pbozeman/vanilla-ice40/examples/gfx/gfx_top.v

`ifndef GFX_TOP_V
`define GFX_TOP_V

// Super basic hello world of a line.
// Output coordinates to io pins, no display, for now.

`include "directives.v"

`include "initial_reset.v"
`include "gfx_line.v"

module gfx_top #(
    parameter VGA_WIDTH  = 640,
    parameter VGA_HEIGHT = 480
) (
    // board signals
    input  wire CLK,
    output wire LED1,
    output wire LED2,

    output wire [7:0] R_E,
    output wire [7:0] R_F,

    output wire [7:0] R_H,
    output wire [7:0] R_I
);
  localparam FB_X_BITS = $clog2(VGA_WIDTH);
  localparam FB_Y_BITS = $clog2(VGA_HEIGHT);

  reg                 reset;

  reg                 enable;
  reg                 start;
  reg [FB_X_BITS-1:0] x0;
  reg [FB_Y_BITS-1:0] y0;
  reg [FB_X_BITS-1:0] x1;
  reg [FB_Y_BITS-1:0] y1;

  reg [FB_X_BITS-1:0] x;
  reg [FB_Y_BITS-1:0] y;
  reg                 done;

  initial_reset u_initial_reset (
      .clk  (CLK),
      .reset(reset)
  );

  gfx_line u_line (
      .clk  (CLK),
      .reset(reset),
      .start(start),
      .x0   (x0),
      .y0   (y0),
      .x1   (x1),
      .y1   (y1),
      .x    (x),
      .y    (y),
      .done (done)
  );

  always @(posedge CLK) begin
    x0    <= 10;
    y0    <= 10;
    x1    <= 100;
    y1    <= 100;
    start <= 1'b1;
  end

  assign LED1     = 1'bz;
  assign LED2     = 1'bz;

  assign R_E[7:0] = x[0:8];
  assign R_F[7:6] = x[9:10];
  assign R_F[5:0] = 6'b000000;

  assign R_H[7:0] = y[0:8];
  assign R_I[7:6] = y[9:10];
  assign R_I[5:0] = 6'b000000;

endmodule

`endif
