pbozeman/vanilla-ice40/rtl/test/vga_pixel_addr_tb.sv

`include "testing.sv"

// maybe check the other modes sometime, but this should be fine.
`ifdef VGA_MODE_640_480_60

`include "vga_pixel_addr.sv"

module vga_pixel_addr_tb;
  localparam H_WHOLE_LINE = `VGA_MODE_H_WHOLE_LINE;
  localparam V_WHOLE_FRAME = `VGA_MODE_V_WHOLE_FRAME;

  logic       clk;
  logic       reset;
  logic [9:0] column;
  logic [9:0] row;

  // TODO: add enable tests
  logic       enable = 1'b1;

  vga_pixel_addr #(
      .H_WHOLE_LINE (H_WHOLE_LINE),
      .V_WHOLE_FRAME(V_WHOLE_FRAME)
  ) uut (
      .clk   (clk),
      .reset (reset),
      .enable(enable),
      .column(column),
      .row   (row)
  );

  initial begin
    forever #5 clk = ~clk;
  end

  `TEST_SETUP(vga_pixel_addr_tb);

  initial begin
    clk   = 0;
    reset = 0;

    // Reset
    reset = 1;
    `ASSERT(column == 0);
    `ASSERT(row == 0);
    @(posedge clk);
    reset = 0;
    `ASSERT(column == 0);
    `ASSERT(row == 0);

    @(posedge clk);
    `ASSERT(column == 1);
    `ASSERT(row == 0);

    @(posedge clk);
    `ASSERT(column == 2);
    `ASSERT(row == 0);

    // Advance to end of line
    repeat (797) @(posedge clk);
    `ASSERT(column == 799);
    `ASSERT(row == 0);

    // Row should roll over
    @(posedge clk);
    `ASSERT(column == 0);
    `ASSERT(row == 1);

    // Advance to next line
    repeat (800) @(posedge clk);
    `ASSERT(column == 0);
    `ASSERT(row == 2);

    // Advance to next line
    repeat (522) repeat (800) @(posedge clk);
    `ASSERT(column == 0);
    `ASSERT(row == 524);

    // Should advance to next frame
    repeat (800) @(posedge clk);
    `ASSERT(column == 0);
    `ASSERT(row == 0);

    $finish;
  end
endmodule
`else
module vga_pixel_addr_tb;
endmodule
`endif
