pbozeman/vanilla-ice40/rtl/test/vga_sync_tb.sv

`include "testing.sv"

// maybe check the other modes sometime, but this should be fine.
`ifdef VGA_MODE_640_480_60
`include "vga_mode.sv"
`include "vga_sync.sv"

module vga_sync_tb;
  localparam H_VISIBLE = `VGA_MODE_H_VISIBLE;
  localparam H_FRONT_PORCH = `VGA_MODE_H_FRONT_PORCH;
  localparam H_SYNC_PULSE = `VGA_MODE_H_SYNC_PULSE;
  localparam H_BACK_PORCH = `VGA_MODE_H_BACK_PORCH;
  localparam H_WHOLE_LINE = `VGA_MODE_H_WHOLE_LINE;

  localparam V_VISIBLE = `VGA_MODE_V_VISIBLE;
  localparam V_FRONT_PORCH = `VGA_MODE_V_FRONT_PORCH;
  localparam V_SYNC_PULSE = `VGA_MODE_V_SYNC_PULSE;
  localparam V_BACK_PORCH = `VGA_MODE_V_BACK_PORCH;
  localparam V_WHOLE_FRAME = `VGA_MODE_V_WHOLE_FRAME;

  logic       clk = 1'b0;
  logic       reset = 1'b0;
  logic       visible;
  logic       hsync;
  logic       vsync;
  logic [9:0] column;
  logic [9:0] row;

  logic [3:0] frames = 0;

  // TODO: add enable tests
  logic       enable = 1'b1;

  vga_sync #(
      .H_VISIBLE    (H_VISIBLE),
      .H_FRONT_PORCH(H_FRONT_PORCH),
      .H_SYNC_PULSE (H_SYNC_PULSE),
      .H_BACK_PORCH (H_BACK_PORCH),
      .H_WHOLE_LINE (H_WHOLE_LINE),

      .V_VISIBLE    (V_VISIBLE),
      .V_FRONT_PORCH(V_FRONT_PORCH),
      .V_SYNC_PULSE (V_SYNC_PULSE),
      .V_BACK_PORCH (V_BACK_PORCH),
      .V_WHOLE_FRAME(V_WHOLE_FRAME)
  ) uut (
      .clk    (clk),
      .reset  (reset),
      .enable (enable),
      .visible(visible),
      .hsync  (hsync),
      .vsync  (vsync),
      .column (column),
      .row    (row)
  );

  // clock generator
  always #1 clk <= ~clk;

  `TEST_SETUP(vga_sync_tb);

  initial begin
    // 3 frames
    repeat (3 * H_WHOLE_LINE * V_WHOLE_FRAME) begin
      @(posedge clk);
    end

    // Make sure we actually did stuff
    @(negedge clk);
    `ASSERT(frames == 3);

    $finish;
  end

  // invariants
  always @(posedge clk) begin
    `ASSERT(column < 800)
    `ASSERT(row < 525)

    // visible should only be on for display area
    if (column < 640 && row < 480) begin
      `ASSERT(visible)
    end else begin
      `ASSERT(!visible)
    end

    // vsync should only be on for lines 490 and 491
    if (row == 490 || row == 491) begin
      // Low active
      `ASSERT(!vsync)
    end else begin
      `ASSERT(vsync)
    end

    // hsync test
    if (column >= 656 && column < 752) begin
      `ASSERT(!hsync)
    end else begin
      `ASSERT(hsync);
    end

    if (row == 524 && column == 799) begin
      frames <= frames + 1;
    end
  end
endmodule
`else
module vga_sync_tb;
endmodule

`endif
