pbozeman/vanilla-ice40/examples/sram_test/pattern_generator.v

`ifndef PATTERN_GENERATOR_V
`define PATTERN_GENERATOR_V

`include "directives.v"

module pattern_generator #(
    parameter integer DATA_BITS = 16
) (
    input wire clk,
    input wire reset,
    input wire next,
    input wire [DATA_BITS-1:0] custom,
    output wire [DATA_BITS-1:0] pattern,
    output reg done = 1'b0,
    output reg [2:0] state = 3'b000
);

  reg [DATA_BITS-1:0] pattern_r = 0;
  assign pattern = pattern_r;

  // State constants
  localparam [2:0]
        STATE_ALL_ZEROS      = 3'b000,
        STATE_ALL_ONES       = 3'b001,
        STATE_ALTERNATING_10 = 3'b010,
        STATE_ALTERNATING_01 = 3'b011,
        STATE_HALF_ONES      = 3'b100,
        STATE_ZEROS_AGAIN    = 3'b101,
        STATE_CUSTOM         = 3'b110,
        STATE_FINAL          = STATE_CUSTOM;

  // Pattern constants
  localparam [DATA_BITS-1:0]
        PATTERN_ALL_ZEROS      = {DATA_BITS{1'b0}},
        PATTERN_ALL_ONES       = {DATA_BITS{1'b1}},
        PATTERN_ALTERNATING_10 = {DATA_BITS/2{2'b10}},
        PATTERN_ALTERNATING_01 = {DATA_BITS/2{2'b01}},
        PATTERN_HALF_ONES      = {DATA_BITS{1'b1}} >> (DATA_BITS / 2);

  always @(posedge next or posedge reset) begin
    if (reset) begin
      state <= STATE_ALL_ZEROS;
      done  <= 1'b0;
    end else begin
      done  <= (state == STATE_FINAL);
      state <= state + 1'b1;
    end
  end

  always @(*) begin
    case (state)
      STATE_ALL_ZEROS:      pattern_r = PATTERN_ALL_ZEROS;
      STATE_ALL_ONES:       pattern_r = PATTERN_ALL_ONES;
      STATE_ALTERNATING_10: pattern_r = PATTERN_ALTERNATING_10;
      STATE_ALTERNATING_01: pattern_r = PATTERN_ALTERNATING_01;
      STATE_HALF_ONES:      pattern_r = PATTERN_HALF_ONES;
      STATE_ZEROS_AGAIN:    pattern_r = PATTERN_ALL_ZEROS;
      STATE_CUSTOM:         pattern_r = custom;
      default:              pattern_r = PATTERN_ALL_ZEROS;
    endcase
  end

endmodule

`endif
