pbozeman/vanilla-ice40/examples/vga/pixel_addr.v

// defaults to 640x480
// http://www.tinyvga.com/vga-timing/640x480@60Hz

// for simulation
`timescale 1ns / 1ps

// avoid undeclared symbols
`default_nettype none

module pixel_addr #(
    parameter H_WHOLE_LINE  = 800,
    parameter V_WHOLE_FRAME = 525
) (
    input clk,
    input reset,
    output [9:0] column,
    output [9:0] row
);

  localparam ENABLE = 1'b1;

  counter #(H_WHOLE_LINE - 1) h_counter (
      clk,
      reset,
      ENABLE,
      column
  );

  counter #(V_WHOLE_FRAME - 1) v_counter (
      clk,
      reset,
      column == H_WHOLE_LINE - 1,
      row
  );

endmodule
